makusets/esphome-toshiba-ab/example_estia.yaml

###############################################################################
# Example ESPHome config for Toshiba Estia heat pump via AB-bus (A0-protocol)
#
# Protocol: Estia A0-protocol at 2400 baud 8E1 (NOT TCC-Link or TU2C)
# Compatible with Toshiba Estia R32 systems. For ESTIA R410A systems, use
# estia_R410A.yaml instead.
###############################################################################

esphome:
  name: toshiba-estia

esp8266:
  board: esp12e

logger:
  baud_rate: 0    # Required to free hardware UART for AB-protocol
  level: DEBUG    # Optional, defaults to DEBUG, set to VERBOSE if diagnosing problems

api:

ota:
  password: "your_ota_password"

wifi:
  ssid: !secret wifi_ssid
  password: !secret wifi_password
  ap:
    ssid: "Toshiba Estia Fallback"
    password: "your_ap_password"

web_server:
  port: 80

external_components:
  - source:
      type: git
      url: https://github.com/makusets/esphome-toshiba-ab
    refresh: 0s

# AB-Bus UART
uart:
  tx_pin: GPIO15    # Adjust for your board variant if different
  rx_pin: GPIO13
  baud_rate: 2400
  parity: EVEN
  rx_buffer_size: 2048

climate:
  - platform: toshiba_ab
    
    # DHW thermostat: Heat enables hot-water production and Off disables it.
    # Its target/current temperatures are the DHW setpoint and tank temperature.
    # The Boost preset in the thermostat controls the Hot Water Boost setting;
    # select None/Normal preset in the thermostat to turn boost off.
    
    name: "Toshiba Estia DHW"
    id: toshiba_estia


    # A second thermostat is created automatically for Zone 1 heat/cool/auto/off and water-outlet temperature.
    # Auto uses Toshiba's heating curve, so it intentionally has no target temperature.
    # Off disables heating/cooling operation only; it leaves DHW enabled.
    # Optionally the name and id can be overriden

    zone1_climate:      # Optionally override thermostat naming and id
      name: "Toshiba Estia Zone 1"
      id: estia_zone1

    # A0-protocol (used by R32 Estia/heat pump models, NOT TCC-Link or TU2C)

    frame_format: a0  #required

    # Optional one-byte addresses, the defaults below may be omitted.
    # remote: 0x40
    # master: 0x00

    # Autonomous polling: query E8:C0 (temperatures) and E8:C1 (operating hours) regularly
    # This is the default setting and can be omitted, uncomment and change to false if you need it for some reason
    # autonomous: true

    # Optional Diagnostic sensors
    connected:
      name: "Estia Connected"  #sensor that monitors the connection to the master is alive
    failed_crcs:
      name: "Estia Failed CRCs"  #sensor that counts failed frames
      
    #read-only enables putting the esp in read-only mode for experimentation or diagnosing, with no comms being sent
    read_only: true             # optional, defaults to false; used for debugging to listen to the traffic on the bus without sending
    read_only_switch:
      name: "Read only"         # optional switch to turn on and off read only mode while the esp is running

    # Setpoints reported by the periodic 03:C6 status frame.
    dhw_setpoint:
      name: "Estia DHW Setpoint"
    zone1_setpoint:
      name: "Estia Zone 1 Setpoint"
    zone2_setpoint:
      name: "Estia Zone 2 Setpoint"

    # System temperatures reported by the periodic E8:C0 response from master
    # These do not need to be queried individually as separate sensors
    # This will not fill if autonomous is set to false
    
    compressor_discharge_temperature:  # TD
      name: "Estia Compressor Discharge Temperature"
    outdoor_temperature:  # TO
      name: "Estia Outdoor Temperature"
    condenser_temperature:  # TC
      name: "Estia Condenser Temperature"
    water_inlet_temperature:  # TWI
      name: "Estia Water Inlet Temperature"
    water_outlet_temperature:  # TWO; also used by the Zone 1 climate entity
      name: "Estia Water Outlet Temperature"
    water_heater_outlet_temperature:  # THO
      name: "Estia Water Heater Outlet Temperature"
    zone2_water_temperature:  # TFI; optional Zone 2 circuit, floor inlet temperature
      name: "Estia Zone 2 Water Temperature"
    dhw_current_temperature:  # TTW; also used by the DHW climate entity
      name: "Estia DHW Temperature"

    # Estia-specific runtime sensors
    # This will not fill if autonomous is set to false
    
    compressor_hours:
      name: "Estia Compressor Hours"
    waterpump_hours:
      name: "Estia Water Pump Hours"
    backup_heater_hours:
      name: "Estia Backup Heater Hours"

    sensors:
      - address: 0x6A           # Required for every sensor added, in this case, electrical current sensor of the external unit
        scale: 0.1              # default 1.0; here we decode raw/10 as current is reported in deciAmps
        interval: 30s           # default 5min
        sensor:
          name: "Estia System Current"  #required

          #all other available options of sensor in esphome:

          unit_of_measurement: "A"  #optional, defaults none
          accuracy_decimals: 2  #optional
          device_class: current  #optional but recommended for HA
          state_class: measurement  #optional but recommended for HA


################# Available Sensors for ESTIA R32 ##################################
#
#  Address            Description
#
#  0x0B	            	Mixing-valve position	
#  0x0E	            	Low pressure
#  0x0F	          		Software version 
#  0x60               Heat exchanger temperature
#  0x63               Compressor Suction Temperature TS
#  0x65               Heat Sink Temperature
#  0x6A	            	Compressor electrical current
#  0x6D               Heat Exchanger Coil Temperature
#  0x70	              Compressor frequency
#  0x72	        	   	Outdoor Fan 1 speed	
#  0x73	        	  	Outdoor Fan 2 speed 
#  0x74	            	Expansion-valve position	
#  0x7A	            	High pressure	
#  0xC0	            	Water flow
#  0xF0               Micro Computer Energized hours
#  0xF1               Hot Water Compressor hours (might be the same as compressor_hours from E8:C1 response)
#  0XF2               Cooling Compressor hours
#  0xF3               Heating Compressor hours
#  0XF5               Hot Water E Heater hours?? not sure what it means
#  0xF6               Back Up Heater hours
#  0xF7               Booster Heater On hours
#
#  Use the logs to determine which sensors report valid data for your unit
#  everytime a sensor response is received, it is logged,
#  an invalid response means sensor is not available
###########################################################################


    # 0-10V demand sensor (shows current demand value 0..15)
    # demand:
    #   name: "Estia 0-10V Demand"

# Optional: 0-10V demand emulation
# Uncomment the sections below to emulate the physical 0-10V interface
# in software. This sends periodic heartbeats as address 0x0041.
# Also set demand_enabled: true in the climate section above.

# number:
#   - platform: template
#     name: "Estia Demand"
#     id: estia_demand
#     min_value: 0
#     max_value: 15
#     step: 1
#     optimistic: true
#     restore_value: true
#     set_action:
#       - lambda: id(toshiba_estia).send_estia_demand((uint8_t)x);


  # - platform: template
  #   name: "Estia Demand Enable"
  #   id: estia_demand_enable
  #   optimistic: true
  #   restore_mode: RESTORE_DEFAULT_OFF
  #   turn_on_action:
  #     - lambda: id(toshiba_estia).set_demand_enabled(true);
  #   turn_off_action:
  #     - lambda: id(toshiba_estia).set_demand_enabled(false);
